devzendo/antenna-analyser/IMG_2940.jpg

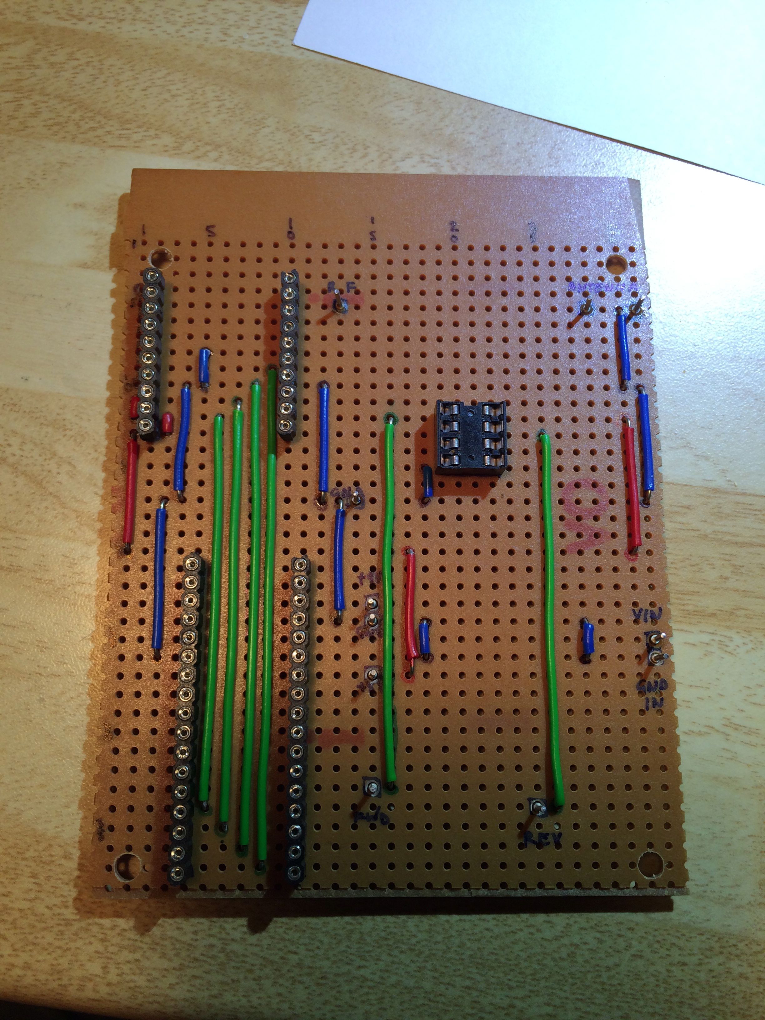
IMG_2940.jpg
