devzendo/antenna-analyser/5VContinuity.png

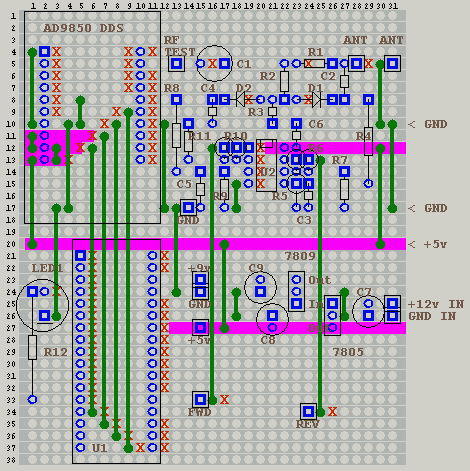
5VContinuity.png
