devzendo/antenna-analyser/AD9850Module.JPG

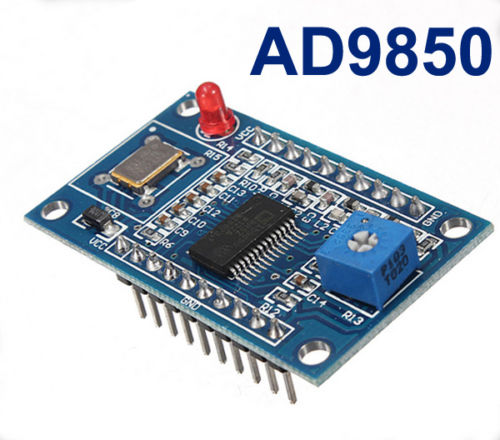
AD9850Module.JPG
