devzendo/antenna-analyser/BericSchematic.png

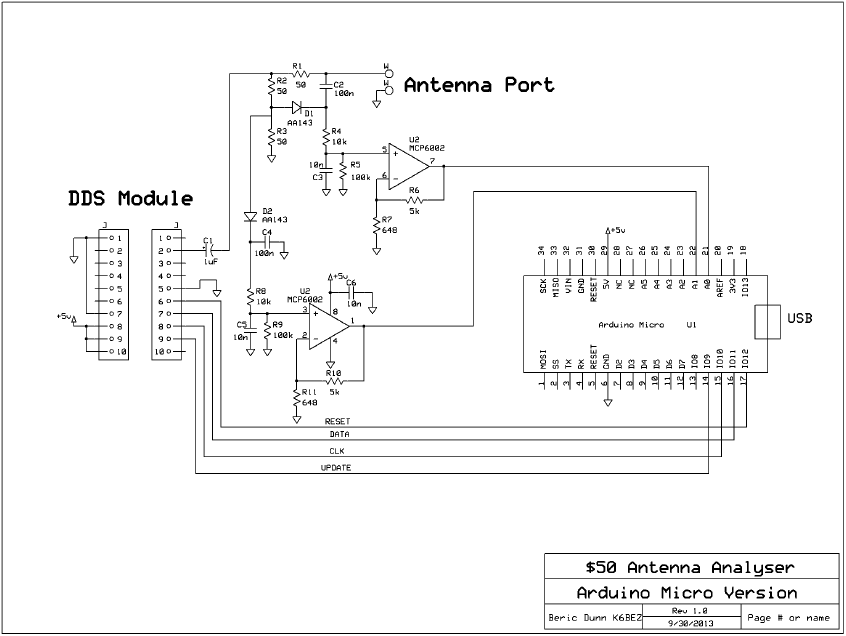
BericSchematic.png
