devzendo/antenna-analyser/IMG_2922.jpg

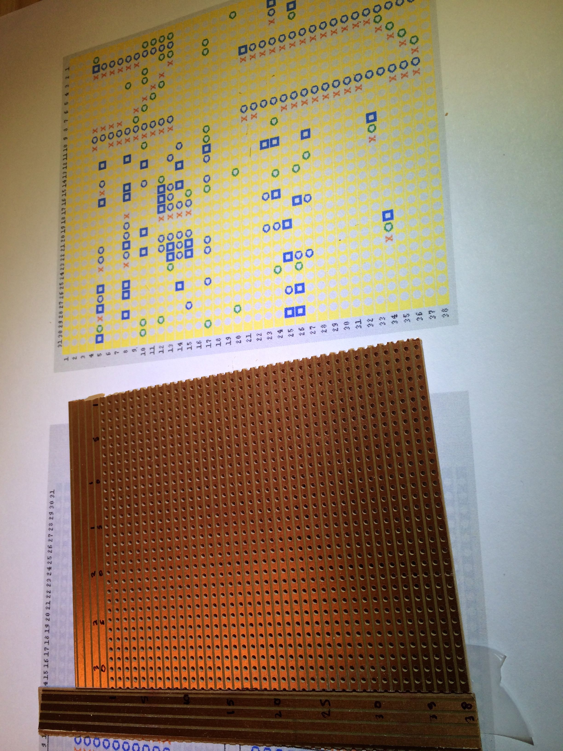
IMG_2922.jpg
