devzendo/antenna-analyser/IMG_2923.jpg

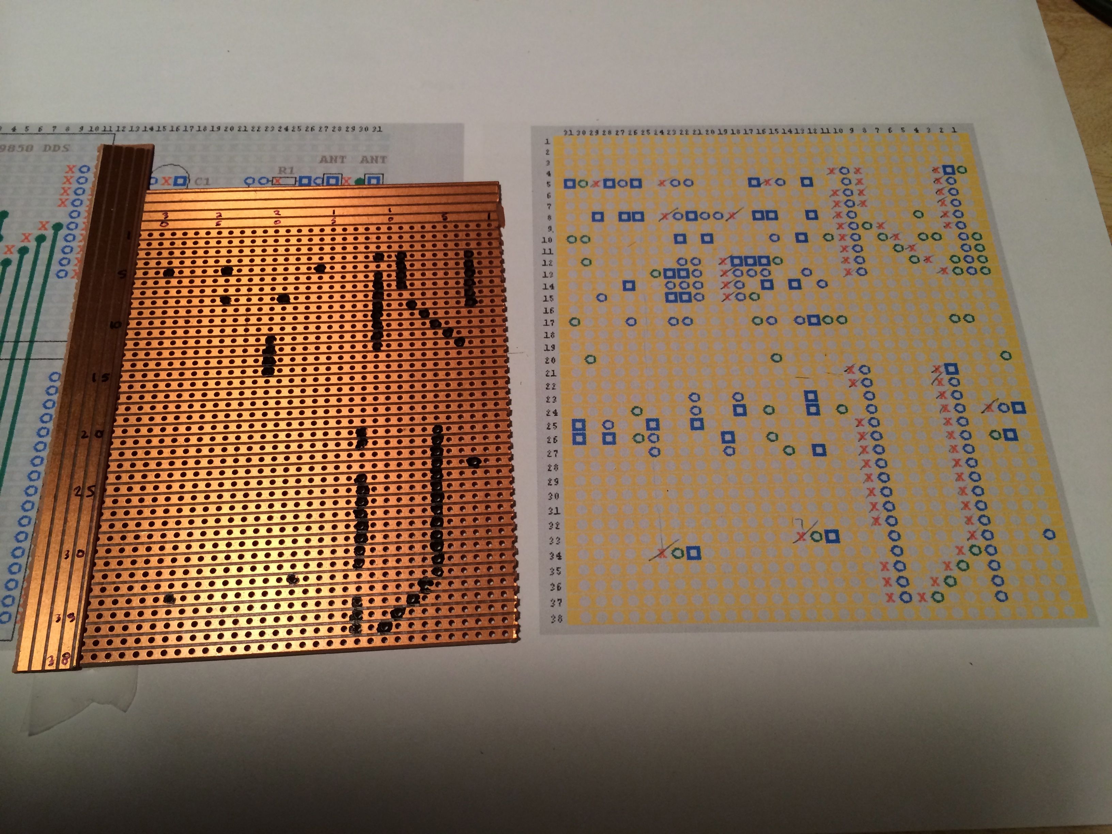
IMG_2923.jpg
