devzendo/antenna-analyser/IMG_2924.jpg

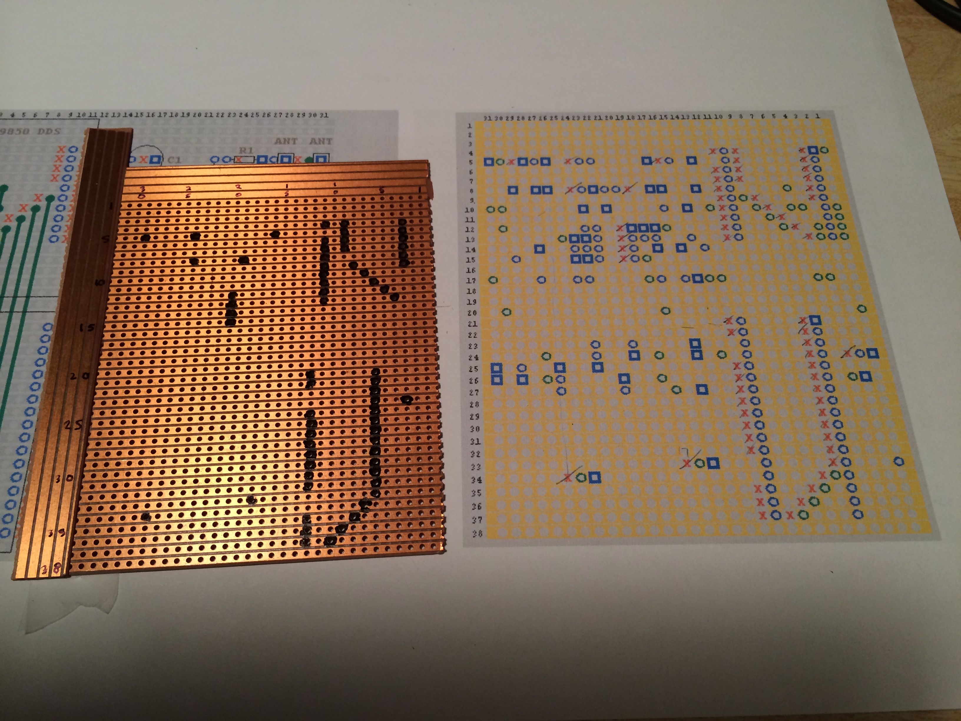
IMG_2924.jpg
