devzendo/antenna-analyser/IMG_2925.jpg

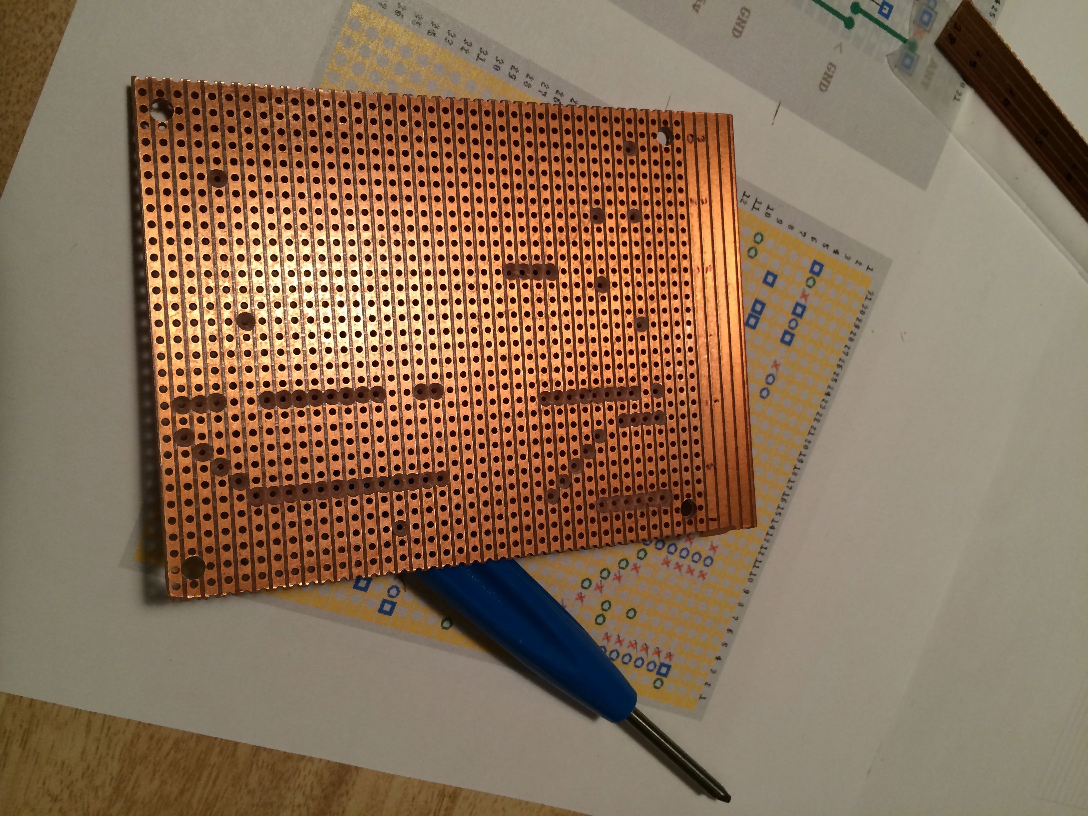
IMG_2925.jpg
