devzendo/antenna-analyser/IMG_2926.jpg

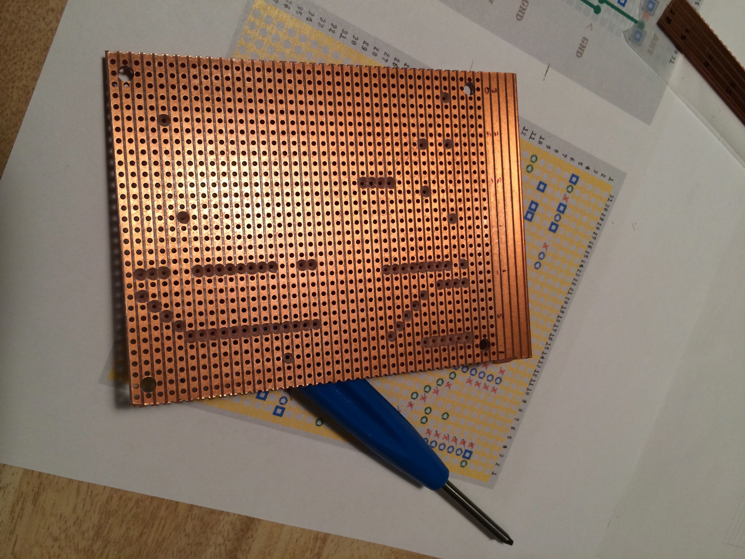
IMG_2926.jpg
