devzendo/antenna-analyser/IMG_2927.jpg

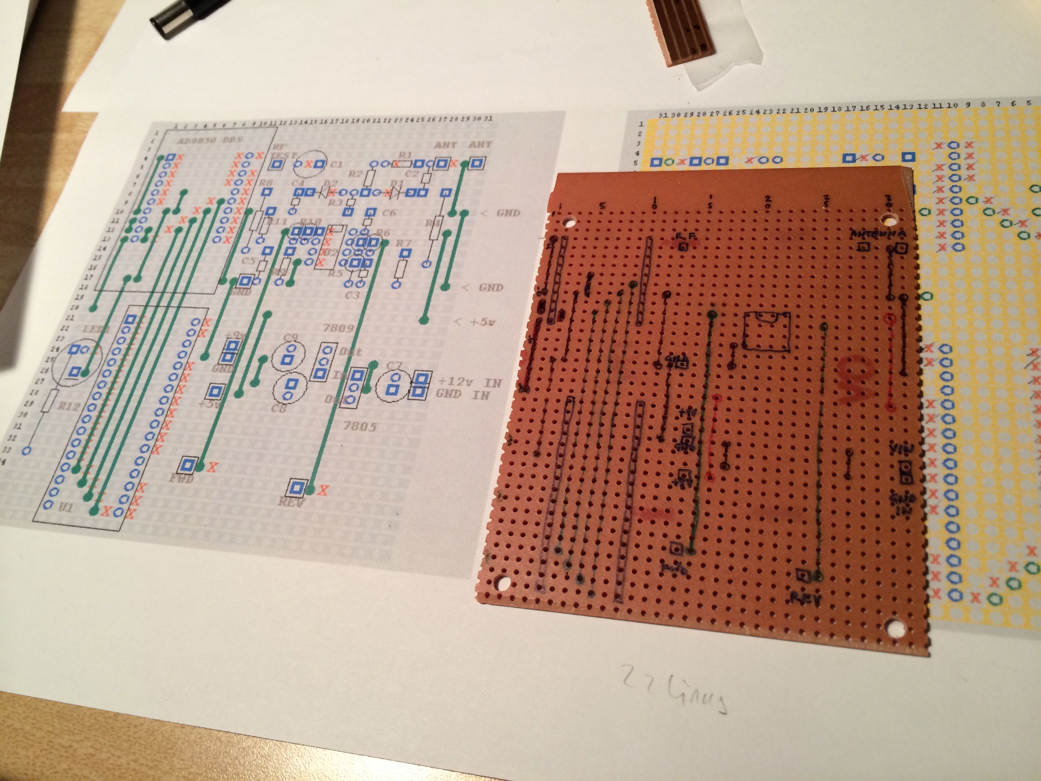
IMG_2927.jpg
