devzendo/antenna-analyser/IMG_2928.jpg

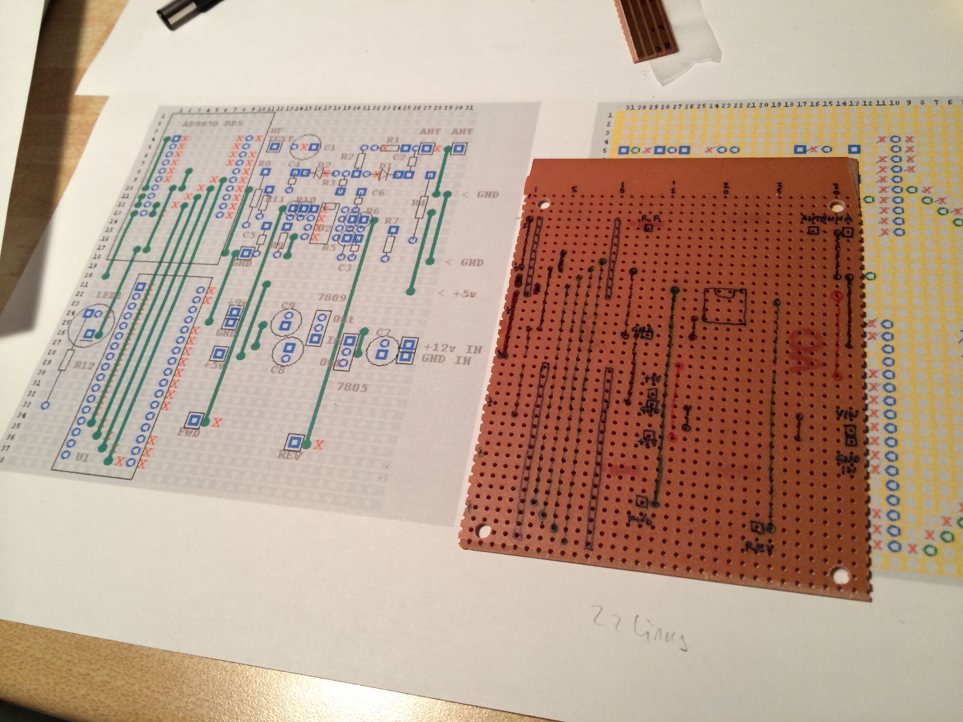
IMG_2928.jpg
