devzendo/antenna-analyser/IMG_2941.jpg

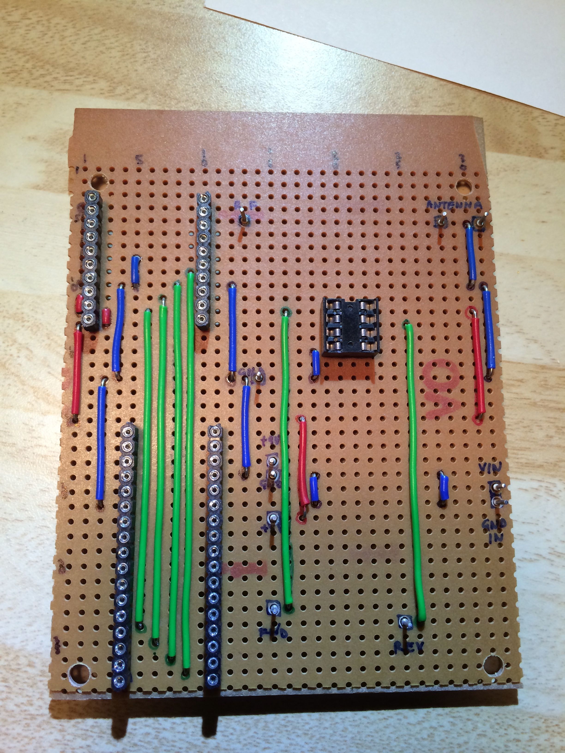
IMG_2941.jpg
