devzendo/antenna-analyser/IMG_2942.jpg

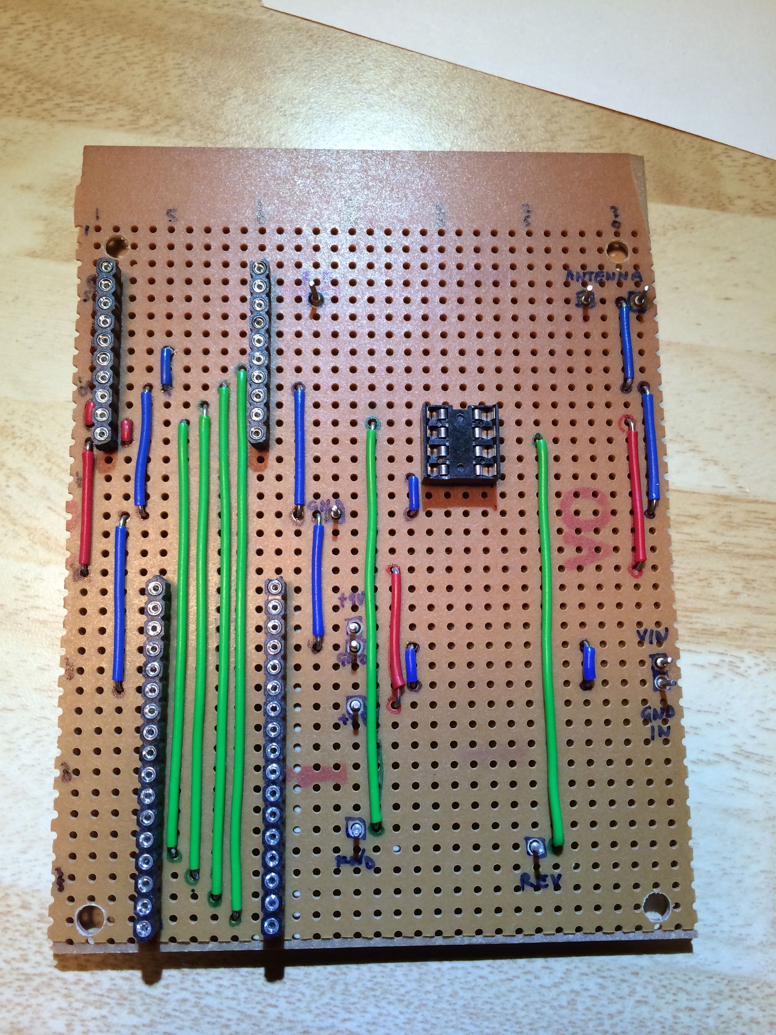
IMG_2942.jpg
