devzendo/antenna-analyser/IMG_2943.jpg

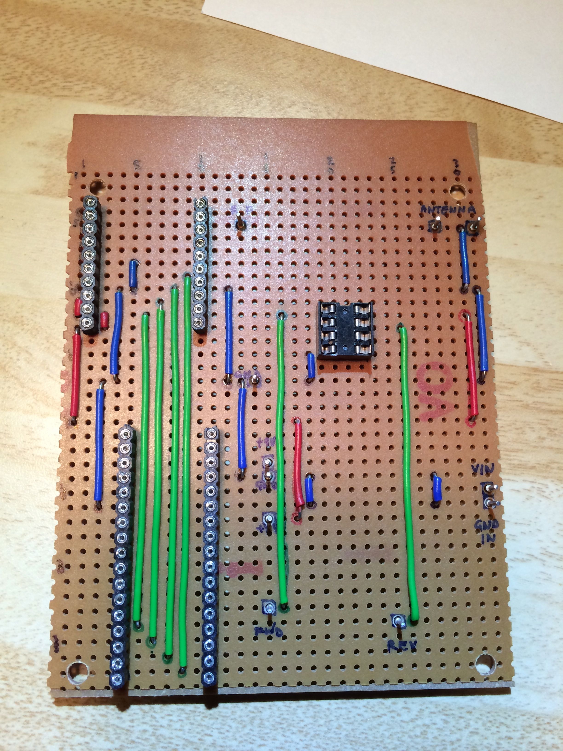
IMG_2943.jpg
