devzendo/antenna-analyser/IMG_2946.jpg

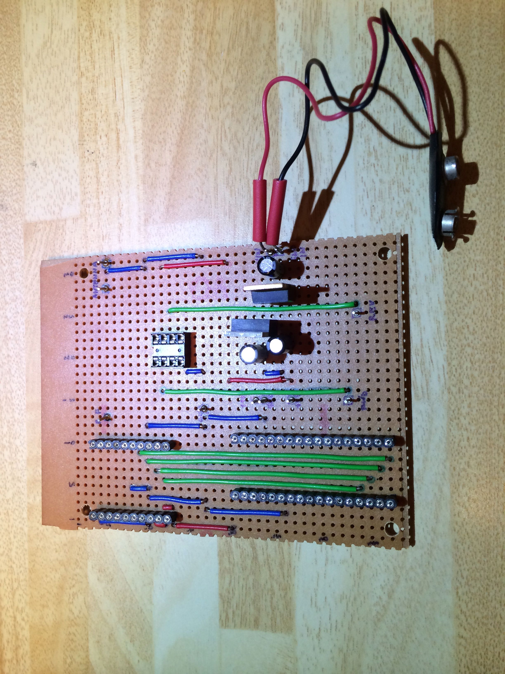
IMG_2946.jpg
