devzendo/antenna-analyser/IMG_2947.jpg

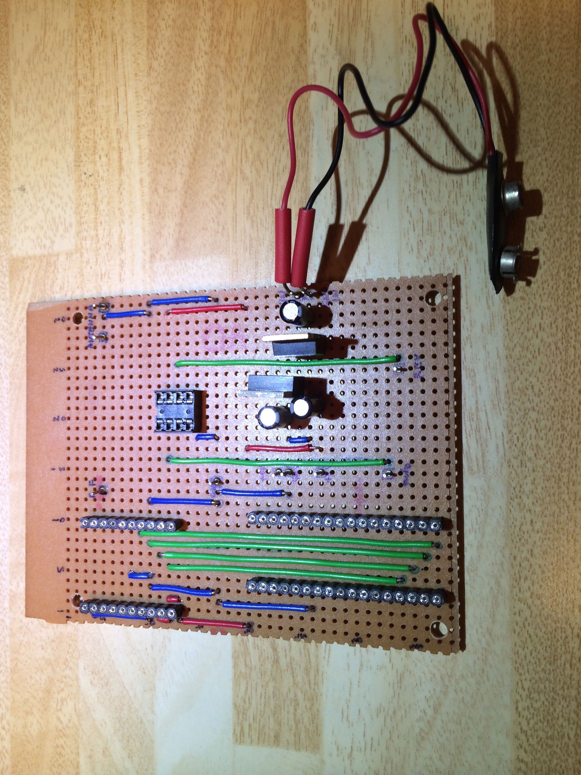
IMG_2947.jpg
