devzendo/antenna-analyser/IMG_2948.jpg

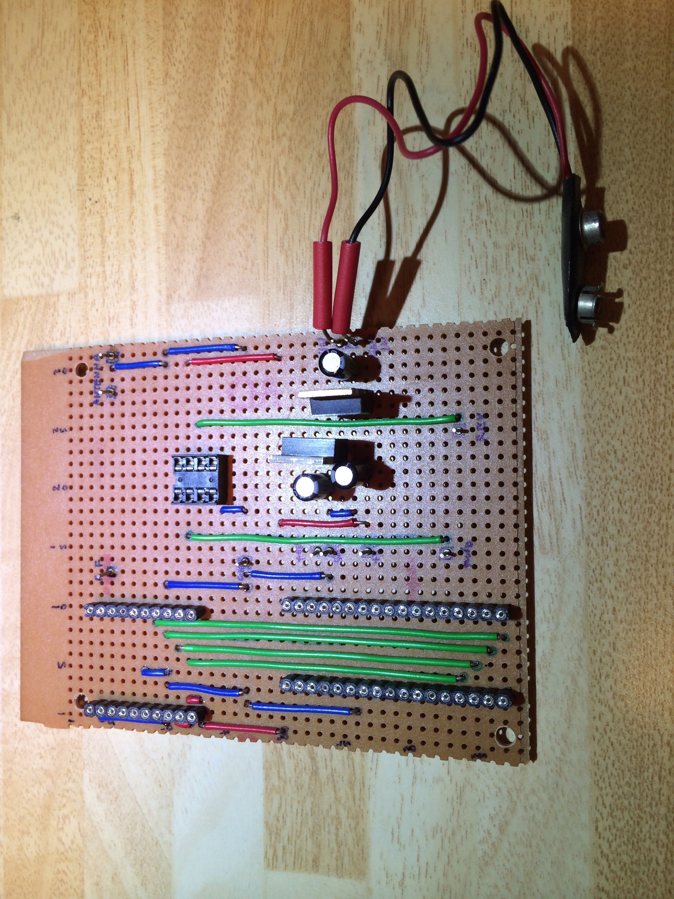
IMG_2948.jpg
