devzendo/antenna-analyser/IMG_2959.jpg

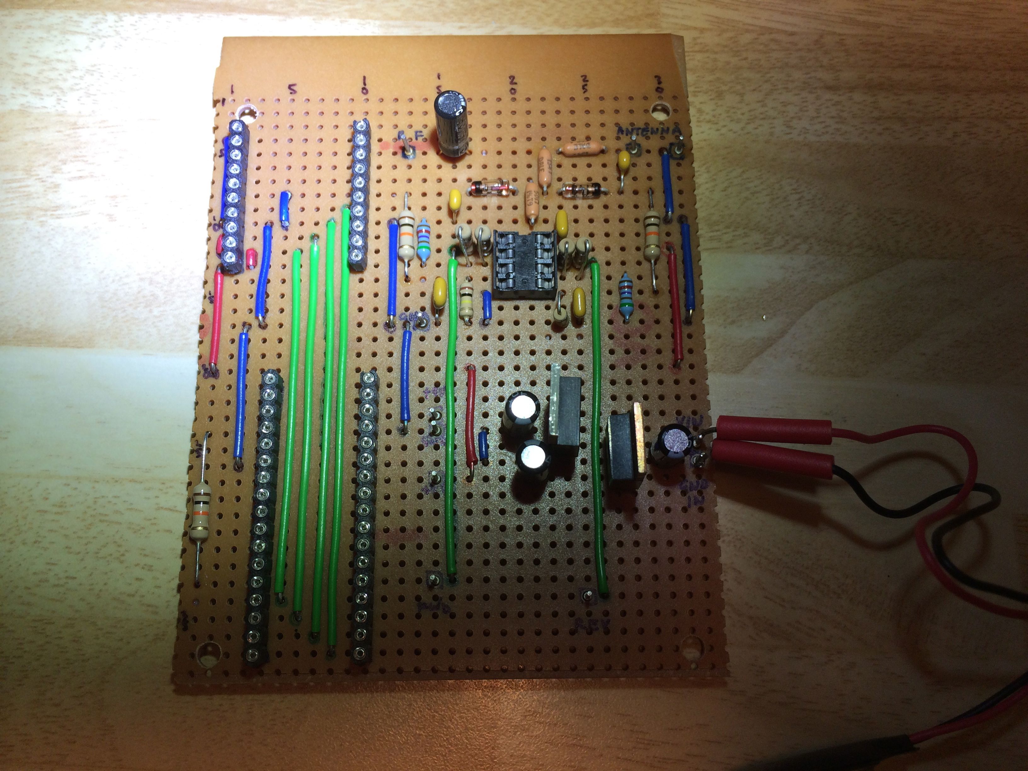
IMG_2959.jpg
