devzendo/antenna-analyser/IMG_2961.jpg

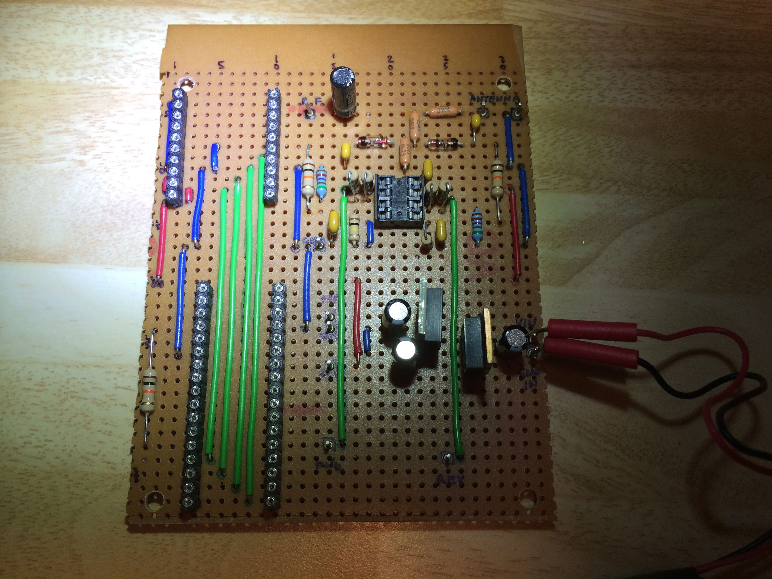
IMG_2961.jpg
