devzendo/antenna-analyser/IMG_2962.jpg

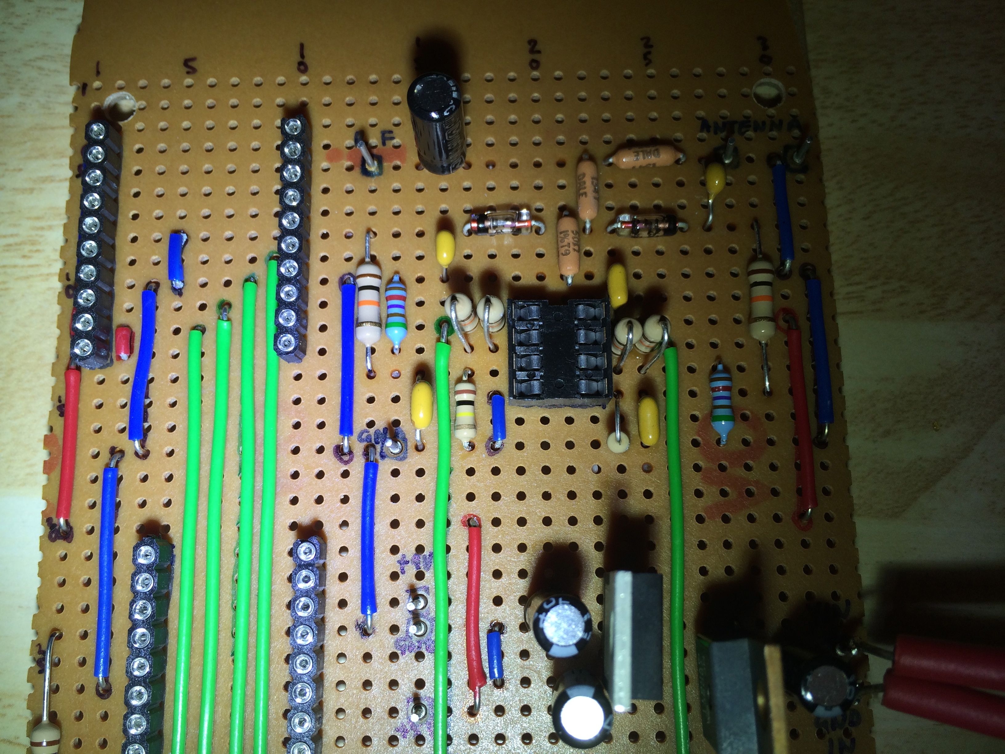
IMG_2962.jpg
