devzendo/antenna-analyser/IMG_2964.jpg

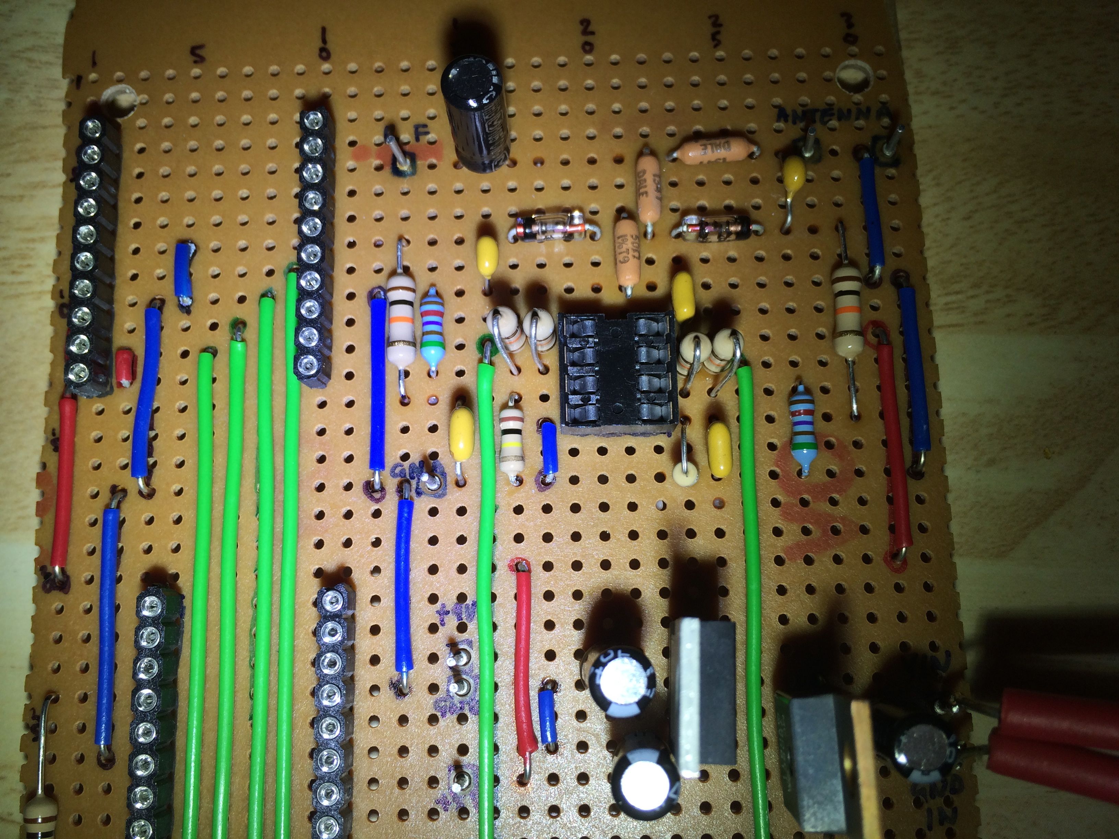
IMG_2964.jpg
