devzendo/antenna-analyser/IMG_2965.jpg

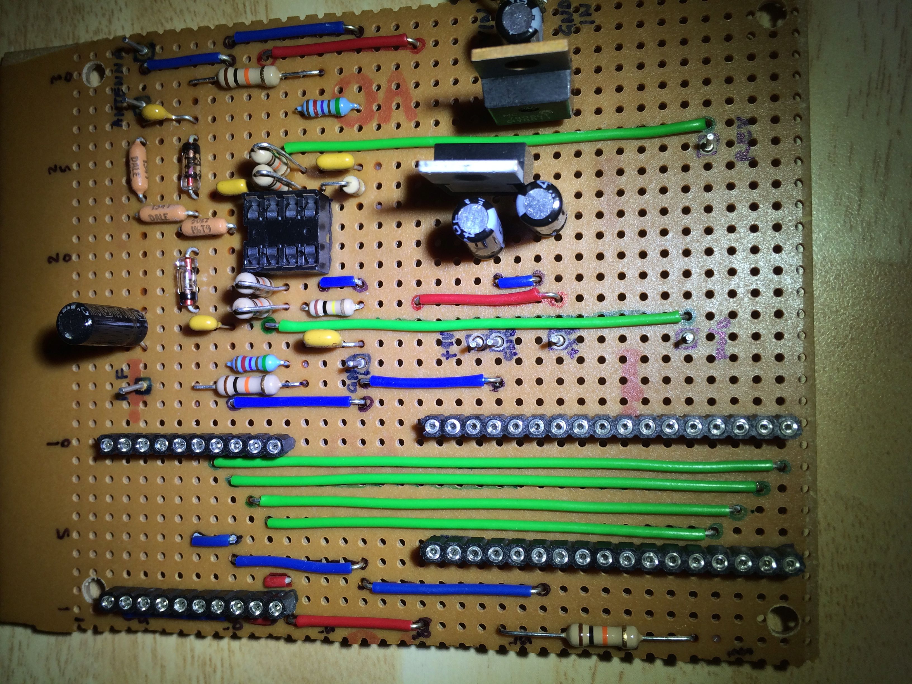
IMG_2965.jpg
