devzendo/antenna-analyser/IMG_2966.jpg

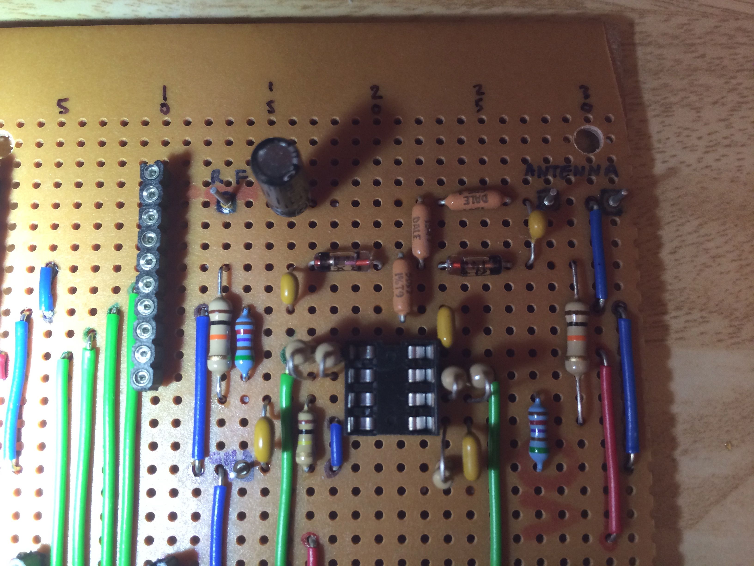
IMG_2966.jpg
