devzendo/antenna-analyser/IMG_2967.jpg

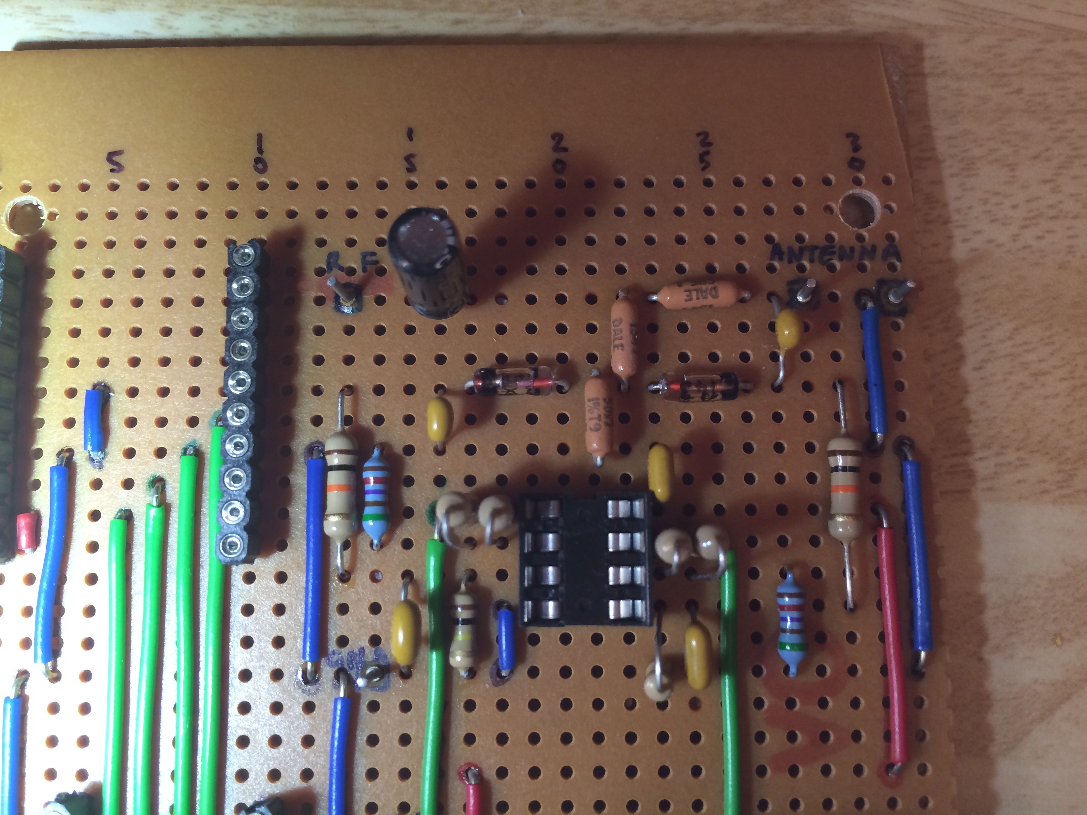
IMG_2967.jpg
