devzendo/antenna-analyser/IMG_2968.jpg

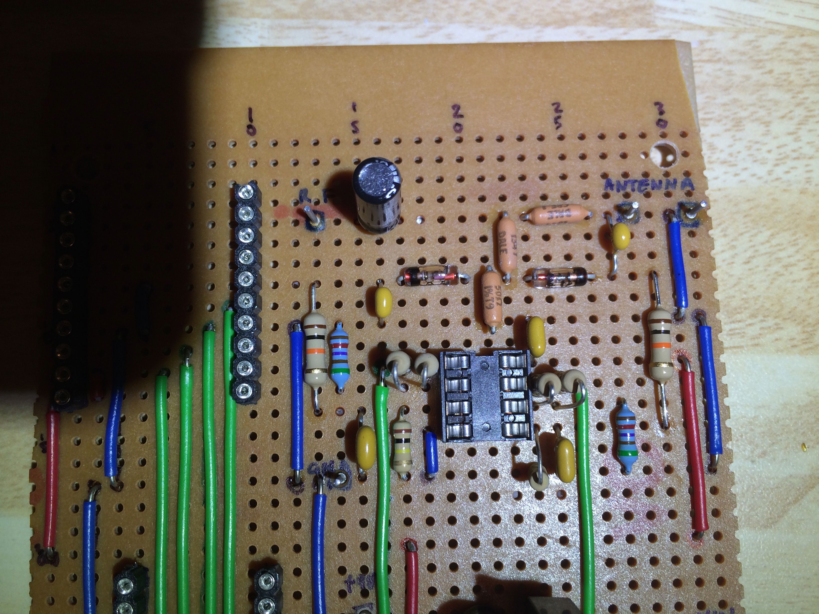
IMG_2968.jpg
