devzendo/antenna-analyser/IMG_2969.jpg

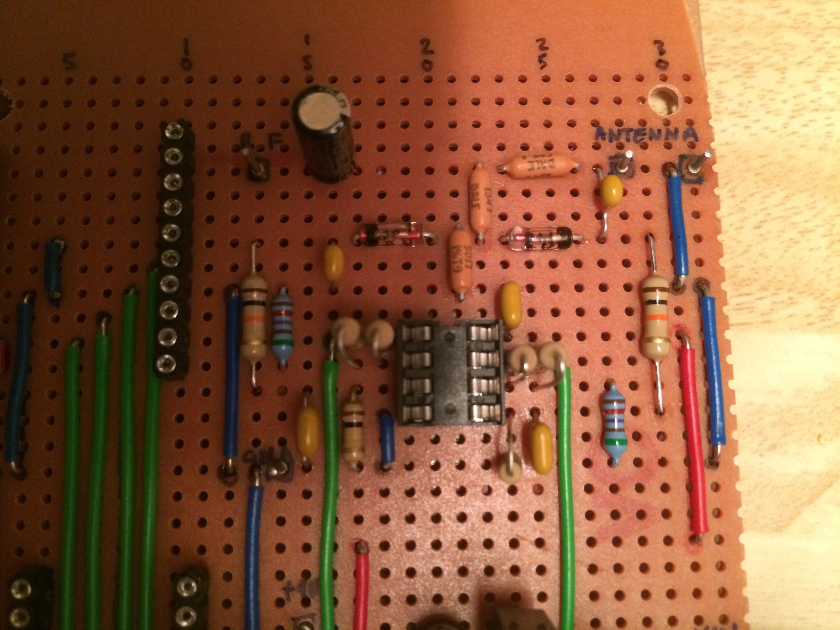
IMG_2969.jpg
