devzendo/antenna-analyser/PhotoBridge.jpg

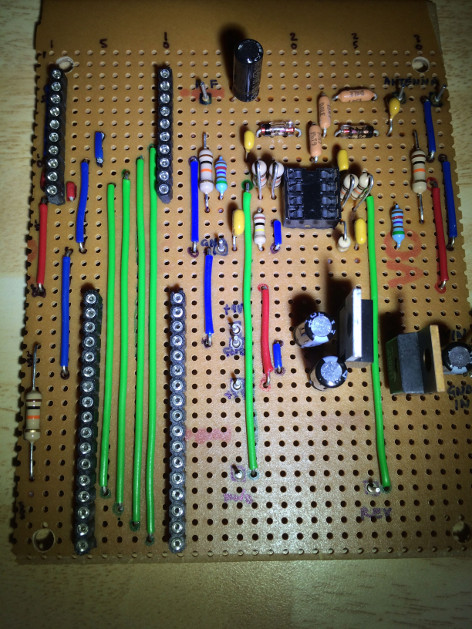
PhotoBridge.jpg
