devzendo/antenna-analyser/PhotoCompleteWithBoards.jpg

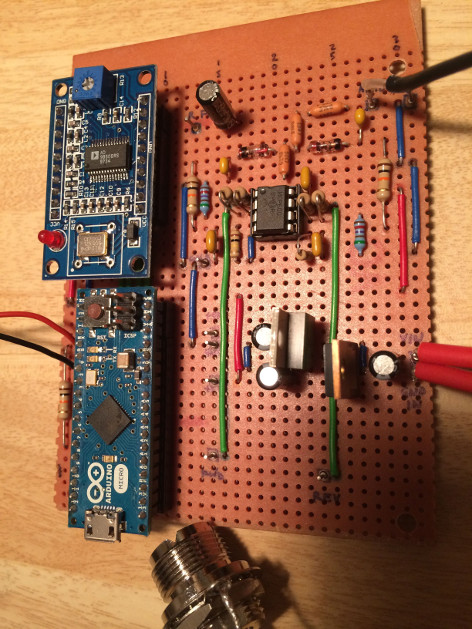
PhotoCompleteWithBoards.jpg
