devzendo/antenna-analyser/PhotoCompleteWithoutBoards.jpg

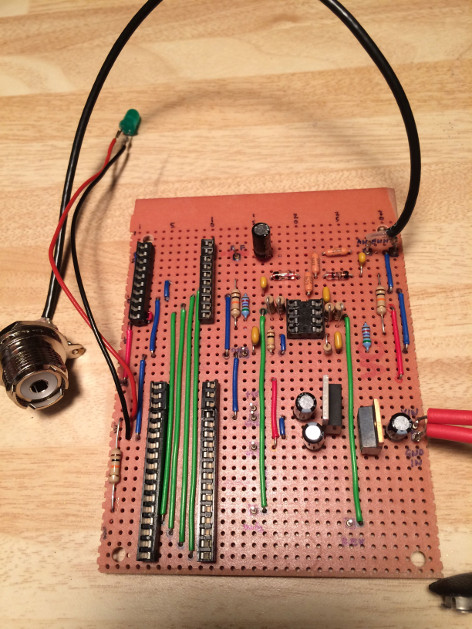
PhotoCompleteWithoutBoards.jpg
