devzendo/antenna-analyser/PhotoEnclosure.png

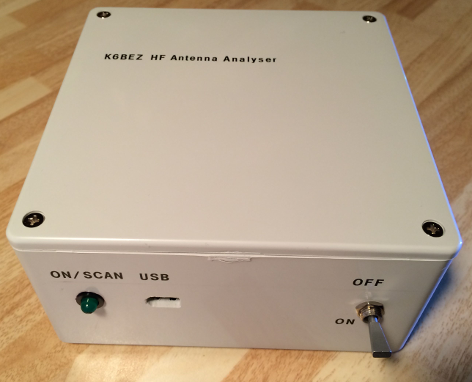
PhotoEnclosure.png
