devzendo/antenna-analyser/PhotoJumpers.jpg

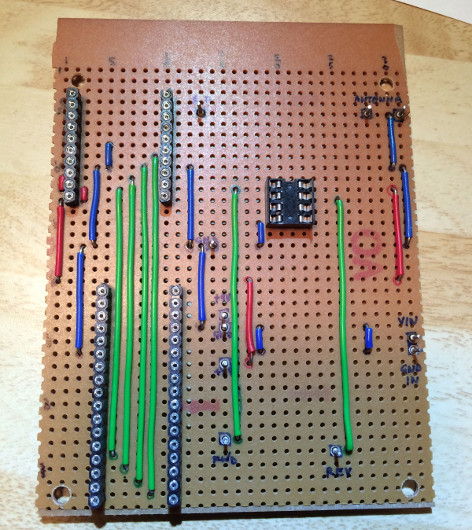
PhotoJumpers.jpg
