devzendo/antenna-analyser/PhotoPower.jpg

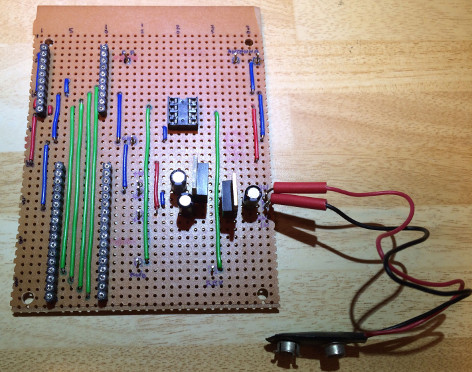
PhotoPower.jpg
