devzendo/antenna-analyser/PhotoSineOutput.jpg

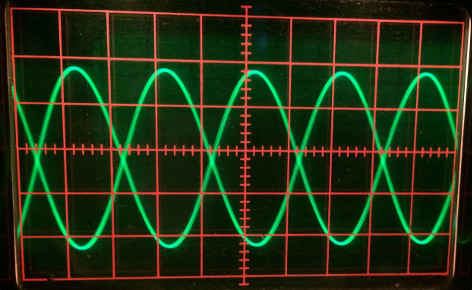
PhotoSineOutput.jpg
