devzendo/antenna-analyser/PhotoTracksCut.jpg

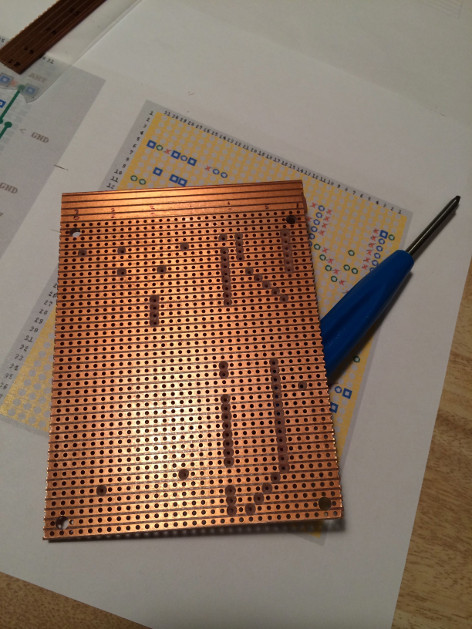
PhotoTracksCut.jpg
