devzendo/antenna-analyser/VeroBoardTrackLayout.png

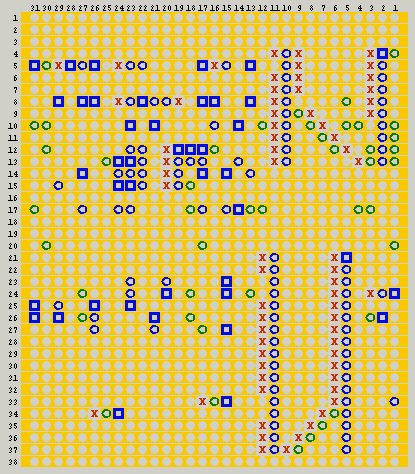
VeroBoardTrackLayout.png
