devzendo/antenna-analyser/VeroBoardComponentLayout.png

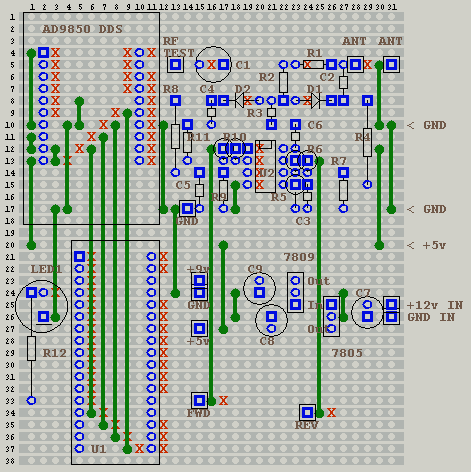
VeroBoardComponentLayout.png
